Jana-Marie/Otter-Iron-PRO/v2.0/img1.png

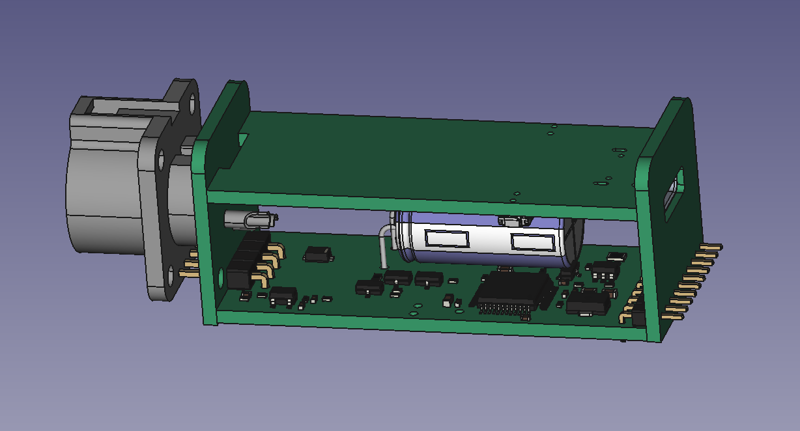
v2.0/img1.png
