Jana-Marie/Otter-Iron-PRO/v2.0/img2.png

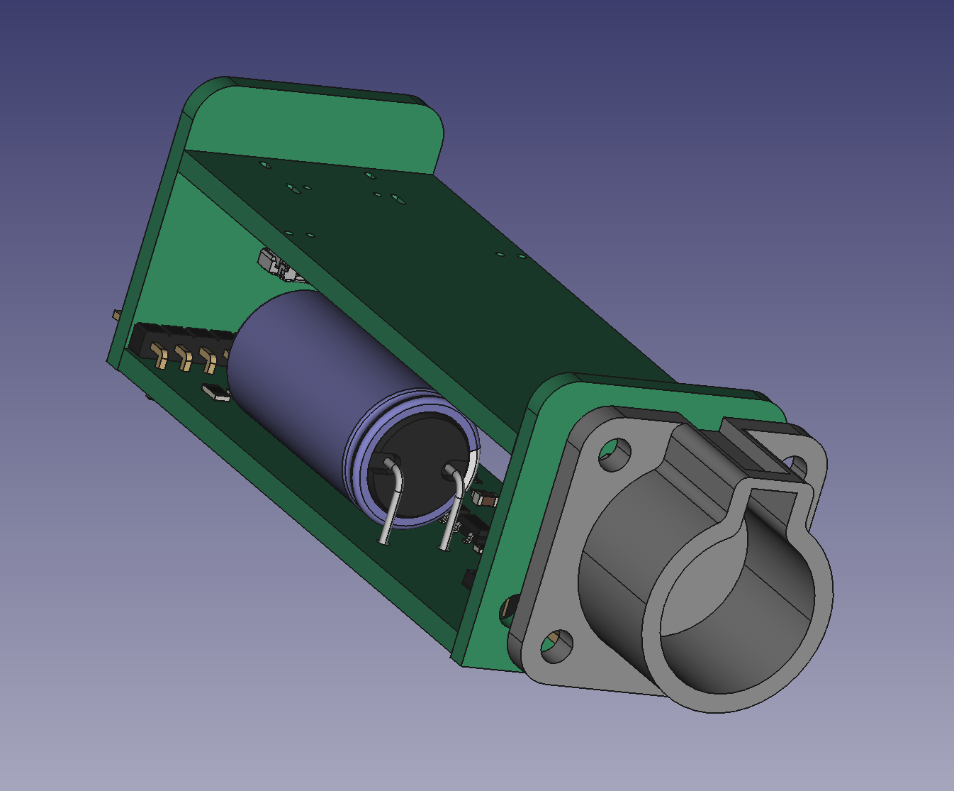
v2.0/img2.png
